blkburn/cc2652_zigbee_zed/zed_sensor_cc2652/Stack/ZStackTask/zstack.h

#define ZSTACK_H
#include <stdbool.h>
#include <stdint.h>
#include "zglobals.h"
#include "nl_mede.h"
#include "bdb_interface.h"
#if !defined (DISABLE_GREENPOWER_BASIC_PROXY) && (ZG_BUILD_RTR_TYPE)
#include "cgp_stub.h"
#endif
#if defined ( BDB_TL_INITIATOR ) || defined ( BDB_TL_TARGET )
#include "bdb_touchlink.h"
#include "bdb_tl_commissioning.h"
#endif
#ifdef __cplusplus
extern "C"
{
#endif
#define EXTADDR_LEN 8
#define DEFAULT_RADIUS  30
#if ZG_BUILD_COORDINATOR_TYPE
#define DEFAULT_COMISSIONING_MODE (BDB_COMMISSIONING_MODE_NWK_STEERING | BDB_COMMISSIONING_MODE_NWK_FORMATION | BDB_COMMISSIONING_MODE_FINDING_BINDING)
#else
#define DEFAULT_COMISSIONING_MODE (BDB_COMMISSIONING_MODE_NWK_STEERING | BDB_COMMISSIONING_MODE_FINDING_BINDING)
#endif
#define BDB_COMMISSIONING_MODE_INITIATOR_TL         (1<<0)
#define BDB_COMMISSIONING_MODE_NWK_STEERING         (1<<1)
#define BDB_COMMISSIONING_MODE_NWK_FORMATION        (1<<2)
#define BDB_COMMISSIONING_MODE_FINDING_BINDING      (1<<3)
typedef enum
{
  zstack_UseDefaultGlobalTrustCenterLinkKey,
  zstack_UseInstallCode,
  zstack_UseInstallCodeWithFallback,
  zstack_UseAPSKey,
  zstack_UseAPSKeyWithFallback,
}zstack_CentralizedLinkKeyModes_t;
typedef enum
{
    zstack_ZStatusValues_ZSuccess = 0x00,
    zstack_ZStatusValues_ZFailure = 0x01,
    zstack_ZStatusValues_ZInvalidParameter = 0x02,
    zstack_ZStatusValues_ZDecodeError = 0x03,
    zstack_ZStatusValues_ZMemError = 0x10,
    zstack_ZStatusValues_ZBufferFull = 0x11,
    zstack_ZStatusValues_ZUnsupportedMode = 0x12,
    zstack_ZStatusValues_ZMacMemError = 0x13,
    zstack_ZStatusValues_ZSapiInProgress = 0x20,
    zstack_ZStatusValues_ZSapiTimeout = 0x21,
    zstack_ZStatusValues_ZSapiInit = 0x22,
    zstack_ZStatusValues_ZNotAuthorized = 0x7E,
    zstack_ZStatusValues_ZMalformedCmd = 0x80,
    zstack_ZStatusValues_ZUnsupClusterCmd = 0x81,
    zstack_ZStatusValues_ZOtaAbort = 0x95,
    zstack_ZStatusValues_ZOtaImageInvalid = 0x96,
    zstack_ZStatusValues_ZOtaWaitForData = 0x97,
    zstack_ZStatusValues_ZOtaNoImageAvailable = 0x98,
    zstack_ZStatusValues_ZOtaRequireMoreImage = 0x99,
    zstack_ZStatusValues_ZApsFail = 0xb1,
    zstack_ZStatusValues_ZApsTableFull = 0xb2,
    zstack_ZStatusValues_ZApsIllegalRequest = 0xb3,
    zstack_ZStatusValues_ZApsInvalidBinding = 0xb4,
    zstack_ZStatusValues_ZApsUnsupportedAttrib = 0xb5,
    zstack_ZStatusValues_ZApsNotSupported = 0xb6,
    zstack_ZStatusValues_ZApsNoAck = 0xb7,
    zstack_ZStatusValues_ZApsDuplicateEntry = 0xb8,
    zstack_ZStatusValues_ZApsNoBoundDevice = 0xb9,
    zstack_ZStatusValues_ZApsNotAllowed = 0xba,
    zstack_ZStatusValues_ZApsNotAuthenticated = 0xbb,
    zstack_ZStatusValues_ZSecNoKey = 0xa1,
    zstack_ZStatusValues_ZSecOldFrmCount = 0xa2,
    zstack_ZStatusValues_ZSecMaxFrmCount = 0xa3,
    zstack_ZStatusValues_ZSecCcmFail = 0xa4,
    zstack_ZStatusValues_ZNwkInvalidParam = 0xc1,
    zstack_ZStatusValues_ZNwkInvalidRequest = 0xc2,
    zstack_ZStatusValues_ZNwkNotPermitted = 0xc3,
    zstack_ZStatusValues_ZNwkStartupFailure = 0xc4,
    zstack_ZStatusValues_ZNwkAlreadyPresent = 0xc5,
    zstack_ZStatusValues_ZNwkSyncFailure = 0xc6,
    zstack_ZStatusValues_ZNwkTableFull = 0xc7,
    zstack_ZStatusValues_ZNwkUnknownDevice = 0xc8,
    zstack_ZStatusValues_ZNwkUnsupportedAttribute = 0xc9,
    zstack_ZStatusValues_ZNwkNoNetworks = 0xca,
    zstack_ZStatusValues_ZNwkLeaveUnconfirmed = 0xcb,
    zstack_ZStatusValues_ZNwkNoAck = 0xcc,
    zstack_ZStatusValues_ZNwkNoRoute = 0xcd,
    zstack_ZStatusValues_ZAfDuplicateEndpoint = 0xd0,
    zstack_ZStatusValues_ZAfEndpointMax = 0xd1,
    zstack_ZStatusValues_ZIcallNoMsg = 0x30,
    zstack_ZStatusValues_ZIcallTimeout = 0x31
} zstack_ZStatusValues;
typedef enum
{
    zstack_AFAddrMode_NONE = 0,
    zstack_AFAddrMode_GROUP = 1,
    zstack_AFAddrMode_SHORT = 2,
    zstack_AFAddrMode_EXT = 3,
    zstack_AFAddrMode_BROADCAST = 15,
} zstack_AFAddrMode;
typedef enum
{
    zstack_ResetTypes_DEVICE = 0,
    zstack_ResetTypes_SERIAL_BOOTLOADER = 1,
} zstack_ResetTypes;
typedef enum
{
    zstack_ResetReasons_POWERUP = 0,
    zstack_ResetReasons_EXTERNAL = 1,
    zstack_ResetReasons_WATCHDOG = 2,
} zstack_ResetReasons;
typedef enum
{
    zstack_LogicalTypes_COORDINATOR = 0,
    zstack_LogicalTypes_ROUTER = 1,
    zstack_LogicalTypes_ENDDEVICE = 2,
    zstack_LogicalTypes_UNKNOWN = 3,
} zstack_LogicalTypes;
typedef enum
{
    zstack_NetworkLatency_NO_LATENCY_REQS = 0,
    zstack_NetworkLatency_FAST_BEACONS = 1,
    zstack_NetworkLatency_SLOW_BEACONDS = 2,
} zstack_NetworkLatency;
typedef enum
{
    zstack_NwkAddrReqType_SINGLE_DEVICE = 0,
    zstack_NwkAddrReqType_EXTENDED_W_ASSOCDEVS = 1,
} zstack_NwkAddrReqType;
typedef enum
{
    zstack_PowerLevel_LEVEL_CRITICAL = 0x00,
    zstack_PowerLevel_LEVEL_33 = 0x04,
    zstack_PowerLevel_LEVEL_66 = 0x08,
    zstack_PowerLevel_LEVEL_100 = 0x0C,
} zstack_PowerLevel;
typedef enum
{
    zstack_PowerModes_POWER_SYNCHRONIZED = 0,
    zstack_PowerModes_POWER_PERIODIC = 1,
    zstack_PowerModes_POWER_STIMULATED = 2,
} zstack_PowerModes;
typedef enum
{
    zstack_ZdpStatus_SUCCESS = 0,
    zstack_ZdpStatus_INVALID_REQTYPE = 0x80,
    zstack_ZdpStatus_DEVICE_NOT_FOUND = 0x81,
    zstack_ZdpStatus_INVALID_EP = 0x82,
    zstack_ZdpStatus_NOT_ACTIVE = 0x83,
    zstack_ZdpStatus_NOT_SUPPORTED = 0x84,
    zstack_ZdpStatus_TIMEOUT = 0x85,
    zstack_ZdpStatus_NO_MATCH = 0x86,
    zstack_ZdpStatus_NO_ENTRY = 0x88,
    zstack_ZdpStatus_NO_DESCRIPTOR = 0x89,
    zstack_ZdpStatus_INSUFFICIENT_SPACE = 0x8a,
    zstack_ZdpStatus_NOT_PERMITTED = 0x8b,
    zstack_ZdpStatus_TABLE_FULL = 0x8c,
    zstack_ZdpStatus_NOT_AUTHORIZED = 0x8d,
    zstack_ZdpStatus_BINDING_TABLE_FULL = 0x8e,
} zstack_ZdpStatus;
typedef enum
{
    zstack_DevState_HOLD = 0,
    zstack_DevState_INIT = 1,
    zstack_DevState_NWK_DISC = 2,
    zstack_DevState_NWK_JOINING = 3,
    zstack_DevState_NWK_REJOIN_SEC_CURR_CHANNEL = 4,
    zstack_DevState_END_DEVICE_UNAUTH = 5,
    zstack_DevState_DEV_END_DEVICE = 6,
    zstack_DevState_DEV_ROUTER = 7,
    zstack_DevState_COORD_STARTING = 8,
    zstack_DevState_DEV_ZB_COORD = 9,
    zstack_DevState_NWK_ORPHAN = 10,
    zstack_DevState_NWK_KA = 11,
    zstack_DevState_NWK_BACKOFF = 12,
    zstack_DevState_NWK_REJOIN_SEC_ALL_CHANNEL = 13,
    zstack_DevState_NWK_TC_REJOIN_CURR_CHANNEL = 14,
    zstack_DevState_NWK_TC_REJOIN_ALL_CHANNEL = 15,
} zstack_DevState;
typedef enum
{
    zstack_NwkState_INIT = 0,
    zstack_NwkState_JOINING_ORPHAN = 1,
    zstack_NwkState_DISC = 2,
    zstack_NwkState_JOINING = 3,
    zstack_NwkState_ENDDEVICE = 4,
    zstack_NwkState_PAN_CHNL_SELECTION = 5,
    zstack_NwkState_PAN_CHNL_VERIFY = 6,
    zstack_NwkState_STARTING = 7,
    zstack_NwkState_ROUTER = 8,
    zstack_NwkState_REJOINING = 9,
} zstack_NwkState;
typedef enum
{
    zstack_RouteStatus_ROUTE_ACTIVE = 0,
    zstack_RouteStatus_ROUTE_DISCOVERY_UNDERWAY = 1,
    zstack_RouteStatus_ROUTE_DISCOVERY_FAILED = 2,
    zstack_RouteStatus_ROUTE_INACTIVE = 3,
    zstack_RouteStatus_ROUTE_VALIDATION_UNDERWAY = 4,
} zstack_RouteStatus;
typedef enum
{
    zstack_RxOnWhenIdleTypes_OFF = 0,
    zstack_RxOnWhenIdleTypes_ON = 1,
    zstack_RxOnWhenIdleTypes_UNKNOWN = 2,
} zstack_RxOnWhenIdleTypes;
typedef enum
{
    zstack_RelationTypes_PARENT = 0,
    zstack_RelationTypes_CHILD = 1,
    zstack_RelationTypes_SIBLING = 2,
    zstack_RelationTypes_UNKNOWN = 3,
    zstack_RelationTypes_PREVIOUS_CHILD = 4,
} zstack_RelationTypes;
typedef enum
{
    zstack_PermitJoinTypes_NOT_ACCEPTING_JOIN = 0,
    zstack_PermitJoinTypes_ACCEPTING_JOIN = 1,
    zstack_PermitJoinTypes_UNKNOWN_JOIN = 2,
} zstack_PermitJoinTypes;
typedef enum
{
    zstack_BuildTypes_COORDINATOR = 0,
    zstack_BuildTypes_ROUTER = 1,
    zstack_BuildTypes_ENDDEVICE = 2,
    zstack_BuildTypes_ALLBUILD = 3,
} zstack_BuildTypes;
typedef uint8_t zstack_LongAddr_t[EXTADDR_LEN];
typedef struct _zstack_afaddr_t
{
    zstack_AFAddrMode addrMode;
    union
    {
        uint16_t shortAddr;
        zstack_LongAddr_t extAddr;
    } addr;
    uint8_t endpoint;
    uint16_t panID;
} zstack_AFAddr_t;
typedef struct _zstack_startupoptions_t
{
    bool clearState;
    bool clearConfig;
} zstack_StartupOptions_t;
typedef struct _zstack_simpledescriptor_t
{
    uint8_t endpoint;
    uint16_t profileID;
    uint16_t deviceID;
    uint8_t deviceVer;
    uint8_t n_inputClusters;
    uint16_t *pInputClusters;
    uint8_t n_outputClusters;
    uint16_t *pOutputClusters;
} zstack_SimpleDescriptor_t;
typedef struct _zstack_transoptions_t
{
    bool wildcardProfileID;
    bool ackRequest;
    bool limitConcentrator;
    bool suppressRouteDisc;
    bool apsSecurity;
    bool skipRouting;
} zstack_TransOptions_t;
typedef struct _zstack_capabilityinfo_t
{
    bool panCoord;
    bool ffd;
    bool mainsPower;
    bool rxOnWhenIdle;
    bool security;
} zstack_CapabilityInfo_t;
typedef struct _zstack_servercapabilities_t
{
    bool primaryTrustCenter;
    bool backupTrustCenter;
    bool primaryBindingTableCache;
    bool backupBindingTableCache;
    bool primaryDiscoveryCache;
    bool backupDiscoveryCache;
    bool networkManager;
} zstack_ServerCapabilities_t;
typedef struct _zstack_bindrec_t
{
    zstack_LongAddr_t srcAddr;
    uint8_t srcEndpoint;
    uint16_t clusterID;
    zstack_AFAddr_t dstAddr;
} zstack_BindRec_t;
typedef struct _zstack_leaveoptions_t
{
    bool rejoin;
    bool removeChildren;
} zstack_LeaveOptions_t;
typedef struct _zstack_nodedescriptor_t
{
    zstack_LogicalTypes logicalType;
    bool complexDescAvail;
    bool userDescAvail;
    uint8_t apsFlags;
    uint8_t freqBand;
    zstack_CapabilityInfo_t capInfo;
    uint16_t manufacturerCode;
    uint8_t maxBufferSize;
    uint16_t maxInTransferSize;
    zstack_ServerCapabilities_t serverMask;
    uint16_t maxOutTransferSize;
    uint32_t descCap;
} zstack_NodeDescriptor_t;
typedef struct _zstack_powersource_t
{
    bool mains;
    bool recharge;
    bool dispose;
} zstack_PowerSource_t;
typedef struct _zstack_powerdescriptor_t
{
    zstack_PowerModes powerMode;
    zstack_PowerSource_t availPowerSource;
    zstack_PowerSource_t currentPowerSource;
    zstack_PowerLevel currentPowerLevel;
} zstack_PowerDescriptor_t;
typedef struct _zstack_nwkdiscitem_t
{
    zstack_LongAddr_t extendedPANID;
    uint8_t logicalChan;
    uint8_t stackProfile;
    uint8_t version;
    uint8_t beaconOrder;
    uint8_t superFrameOrder;
    bool permitJoin;
} zstack_nwkDiscItem_t;
typedef struct _zstack_nwklqiitem_t
{
    uint16_t nwkAddr;
    uint16_t panID;
    zstack_LongAddr_t extendedPANID;
    zstack_LongAddr_t extendedAddr;
    uint8_t rxLqi;
    zstack_LogicalTypes deviceType;
    zstack_RxOnWhenIdleTypes rxOnWhenIdle;
    zstack_RelationTypes relationship;
    uint8_t depth;
    zstack_PermitJoinTypes permit;
} zstack_nwkLqiItem_t;
typedef struct _zstack_routeitem_t
{
    uint16_t dstAddr;
    uint16_t nextHop;
    zstack_RouteStatus status;
    bool memoryConstrained;
    bool manyToOne;
    bool routeRecordRequired;
} zstack_routeItem_t;
typedef struct _zstack_binditem_t
{
    zstack_LongAddr_t srcAddr;
    uint8_t srcEndpoint;
    uint16_t clustedID;
    zstack_AFAddr_t dstAddr;
} zstack_bindItem_t;
typedef struct _zstack_devicetypes_t
{
    bool coodinator;
    bool router;
    bool enddevice;
} zstack_deviceTypes_t;
typedef struct _zstack_sysresetreq_t
{
    zstack_ResetTypes type;
    bool newNwkState;
} zstack_sysResetReq_t;
typedef struct _zstack_sysconfigreadreq_t
{
    bool preConfigKeyEnable;
    bool securityModeEnable;
    bool useDefaultTCLK;
    bool disabledPollRate;
    bool pollRate;
    bool apsAckWaitDuration;
    bool bindingTime;
    bool panID;
    bool maxMissingMacAckLinkFailure;
    bool indirectMsgTimeout;
    bool apsFrameRetries;
    bool bcastRetries;
    bool passiveAckTimeout;
    bool bcastDeliveryTime;
    bool routeExpiryTime;
    bool userDesc;
    bool preConfigKey;
    bool chanList;
    bool multicastRadius;
    bool extendedPANID;
    bool ieeeAddr;
    bool macRxOnIdle;
    bool snifferFeature;
    bool concentratorEnable;
    bool concentratorDiscTime;
    bool nwkUseMultiCast;
    bool devPartOfNetwork;
} zstack_sysConfigReadReq_t;
typedef struct _zstack_sysconfigwritereq_t
{
    bool has_preConfigKeyEnable;
    bool preConfigKeyEnable;
    bool has_securityModeEnable;
    bool securityModeEnable;
    bool has_useDefaultTCLK;
    bool useDefaultTCLK;
    bool has_disablePollRate;
    bool disablePollRate;
    bool has_pollRate;
    uint32_t pollRate;
    uint16_t pollRateType;
    bool has_apsAckWaitDuration;
    uint16_t apsAckWaitDuration;
    bool has_bindingTime;
    uint16_t bindingTime;
    bool has_panID;
    uint16_t panID;
    bool has_maxMissingMacAckLinkFailure;
    uint8_t maxMissingMacAckLinkFailure;
    bool has_indirectMsgTimeout;
    uint8_t indirectMsgTimeout;
    bool has_apsFrameRetries;
    uint8_t apsFrameRetries;
    bool has_bcastRetries;
    uint8_t bcastRetries;
    bool has_passiveAckTimeout;
    uint8_t passiveAckTimeout;
    bool has_bcastDeliveryTime;
    uint8_t bcastDeliveryTime;
    bool has_routeExpiryTime;
    uint8_t routeExpiryTime;
    bool has_userDesc;
    uint8_t n_userDesc;
    uint8_t *pUserDesc;
    bool has_preConfigKey;
    uint8_t n_preConfigKey;
    uint8_t *pPreConfigKey;
    bool has_chanList;
    uint32_t chanList;
    bool has_multicastRadius;
    uint8_t multicastRadius;
    bool has_extendedPANID;
    zstack_LongAddr_t extendedPANID;
    bool has_ieeeAddr;
    zstack_LongAddr_t ieeeAddr;
    bool has_macRxOnIdle;
    bool macRxOnIdle;
    bool has_snifferFeature;
    bool snifferFeature;
    bool has_concentratorEnable;
    bool concentratorEnable;
    bool has_concentratorDiscTime;
    uint8_t concentratorDiscTime;
    bool has_nwkUseMultiCast;
    bool nwkUseMultiCast;
} zstack_sysConfigWriteReq_t;
typedef struct _zstack_syssettxpowerreq_t
{
    int_least8_t requestedTxPower;
} zstack_sysSetTxPowerReq_t;
typedef struct _zstack_sysversionrsp_t
{
    uint8_t transportRev;
    zstack_BuildTypes product;
    uint8_t majorRel;
    uint8_t minorRel;
    uint8_t maintRel;
} zstack_sysVersionRsp_t;
typedef struct _zstack_sysconfigreadrsp_t
{
    bool has_preConfigKeyEnable;
    bool preConfigKeyEnable;
    bool has_securityModeEnable;
    bool securityModeEnable;
    bool has_useDefaultTCLK;
    bool useDefaultTCLK;
    bool has_disabledPollRateState;
    bool disabledPollRate;
    bool has_pollRate;
    uint32_t CurrentPollRate;
    uint16_t CurrentPollRateTypesEnabled;
    uint32_t PollRateDefault;
    uint32_t PollRateApp1;
    uint32_t PollRateApp2;
    uint32_t PollRateJoinRejoin;
    uint32_t PollRateQueue;
    uint32_t PollRateResponse;
    bool has_apsAckWaitDuration;
    uint16_t apsAckWaitDuration;
    bool has_bindingTime;
    uint16_t bindingTime;
    bool has_panID;
    uint16_t panID;
    bool has_maxMissingMacAckLinkFailure;
    uint8_t maxMissingMacAckLinkFailure;
    bool has_indirectMsgTimeout;
    uint8_t indirectMsgTimeout;
    bool has_apsFrameRetries;
    uint8_t apsFrameRetries;
    bool has_bcastRetries;
    uint8_t bcastRetries;
    bool has_passiveAckTimeout;
    uint8_t passiveAckTimeout;
    bool has_bcastDeliveryTime;
    uint8_t bcastDeliveryTime;
    bool has_routeExpiryTime;
    uint8_t routeExpiryTime;
    bool has_userDesc;
    uint8_t n_userDesc;
    uint8_t *pUserDesc;
    bool has_preConfigKey;
    uint8_t *pPreConfigKey;
    bool has_chanList;
    uint32_t chanList;
    bool has_multicastRadius;
    uint8_t multicastRadius;
    bool has_extendedPANID;
    zstack_LongAddr_t extendedPANID;
    bool has_ieeeAddr;
    zstack_LongAddr_t ieeeAddr;
    bool has_macRxOnIdle;
    bool macRxOnIdle;
    bool has_snifferFeature;
    bool snifferFeature;
    bool has_concentratorEnable;
    bool concentratorEnable;
    bool has_concentratorDiscTime;
    uint8_t concentratorDiscTime;
    bool has_nwkUseMultiCast;
    bool nwkUseMultiCast;
    bool has_devPartOfNetwork;
    bool devPartOfNetwork;
} zstack_sysConfigReadRsp_t;
typedef struct _zstack_syssettxpowerrsp_t
{
    int_least8_t txPower;
} zstack_sysSetTxPowerRsp_t;
typedef struct _zstack_sysnwkinforeadrsp_t
{
    uint16_t nwkAddr;
    zstack_LongAddr_t ieeeAddr;
    zstack_DevState devState;
    uint16_t panId;
    zstack_LongAddr_t extendedPanId;
    uint16_t parentNwkAddr;
    zstack_LongAddr_t parentExtAddr;
    zstack_deviceTypes_t devTypes;
    uint8_t logicalChannel;
    zstack_CapabilityInfo_t capInfo;
} zstack_sysNwkInfoReadRsp_t;
typedef struct _zstack_sysAppMsg_t
{
    uint8_t dstEndpoint;
    uint8_t appDataLen;
    uint8_t *pAppData;
} zstack_sysAppMsg_t;
typedef struct _zstack_sysOtaMsg_t
{
    uint8_t cmd;
    uint8_t *pData;
} zstack_sysOtaMsg_t;
typedef struct _zstack_devstartreq_t
{
    uint16_t startDelay;
} zstack_devStartReq_t;
typedef struct _zstack_devnwkdiscreq_t
{
    uint32_t scanChannels;
    uint8_t scanDuration;
} zstack_devNwkDiscReq_t;
typedef struct zstack_setnwkframefwdnotificationreq_t
{
    uint8_t Enabled;
} zstack_setNwkFrameFwdNotificationReq_t;
typedef struct _zstack_devjoinreq_t
{
    uint8_t logicalChannel;
    uint16_t panID;
    zstack_LongAddr_t extendedPANID;
    uint16_t chosenParent;
    uint8_t parentDepth;
    uint8_t stackProfile;
} zstack_devJoinReq_t;
typedef struct _zstack_devrejoinreq_t
{
    bool unsecure;
    uint8_t logicalChannel;
    zstack_LongAddr_t extendedPANID;
} zstack_devRejoinReq_t;
typedef struct _zstack_devzdocbreq_t
{
    bool has_srcRtgIndCB;
    bool srcRtgIndCB;
    bool has_concentratorIndCb;
    bool concentratorIndCb;
    bool has_nwkDiscCnfCB;
    bool nwkDiscCnfCB;
    bool has_beaconNotIndCB;
    bool beaconNotIndCB;
    bool has_joinCnfCB;
    bool joinCnfCB;
    bool has_leaveCnfCB;
    bool leaveCnfCB;
    bool has_leaveIndCB;
    bool leaveIndCB;
    bool has_nwkAddrRsp;
    bool nwkAddrRsp;
    bool has_ieeeAddrRsp;
    bool ieeeAddrRsp;
    bool has_nodeDescRsp;
    bool nodeDescRsp;
    bool has_powerDescRsp;
    bool powerDescRsp;
    bool has_simpleDescRsp;
    bool simpleDescRsp;
    bool has_activeEndpointRsp;
    bool activeEndpointRsp;
    bool has_matchDescRsp;
    bool matchDescRsp;
    bool has_complexDescRsp;
    bool complexDescRsp;
    bool has_userDescRsp;
    bool userDescRsp;
    bool has_discoveryCacheRsp;
    bool discoveryCacheRsp;
    bool has_userDescCnf;
    bool userDescCnf;
    bool has_serverDiscoveryRsp;
    bool serverDiscoveryRsp;
    bool has_bindRsp;
    bool bindRsp;
    bool has_endDeviceBindRsp;
    bool endDeviceBindRsp;
    bool has_unbindRsp;
    bool unbindRsp;
    bool has_mgmtNwkDiscRsp;
    bool mgmtNwkDiscRsp;
    bool has_mgmtLqiRsp;
    bool mgmtLqiRsp;
    bool has_mgmtRtgRsp;
    bool mgmtRtgRsp;
    bool has_mgmtBindRsp;
    bool mgmtBindRsp;
    bool has_mgmtLeaveRsp;
    bool mgmtLeaveRsp;
    bool has_mgmtDirectJoinRsp;
    bool mgmtDirectJoinRsp;
    bool has_mgmtPermitJoinRsp;
    bool mgmtPermitJoinRsp;
    bool has_mgmtNwkUpdateNotify;
    bool mgmtNwkUpdateNotify;
    bool has_deviceAnnounce;
    bool deviceAnnounce;
    bool has_devStateChange;
    bool devStateChange;
    bool has_devJammerInd;
    bool devJammerInd;
    bool has_tcDeviceInd;
    bool tcDeviceInd;
    bool has_devPermitJoinInd;
    bool devPermitJoinInd;
} zstack_devZDOCBReq_t;
typedef struct _zstack_devnwkroutereq_t
{
    uint16_t dstAddr;
    bool mtoRoute;
    bool mtoNoCache;
    bool multicast;
    uint8_t radius;
} zstack_devNwkRouteReq_t;
typedef struct _zstack_devnwkcheckroutereq_t
{
    uint16_t dstAddr;
    bool mtoRoute;
} zstack_devNwkCheckRouteReq_t;
typedef struct _zstack_devjammerind_t
{
    bool jammed;
} zstack_devJammerInd_t;
typedef struct _zstack_devpermitjoinind_t
{
    uint8_t duration;
} zstack_devPermitJoinInd_t;
typedef struct _zstack_devupdateneighbortxcostreq_t
{
    uint16_t nwkAddr;
    uint16_t panID;
    uint8_t txCost;
} zstack_devUpdateNeighborTxCostReq_t;
typedef struct _zstack_devforcenetworksettingsreq_t
{
    zstack_NwkState state;
    uint16_t nwkAddr;
    uint32_t channelList;
    uint16_t parentNwkAddr;
    uint16_t panID;
    uint8_t depth;
    uint8_t maxRouters;
    uint8_t maxChildren;
    uint32_t allocatedRouterAddresses;
    uint32_t allocatedEndDeviceAddresses;
    uint8_t updateID;
    zstack_LongAddr_t extendedPANID;
} zstack_devForceNetworkSettingsReq_t;
typedef struct _zstack_devforcenetworkupdatereq_t
{
    uint8_t updateID;
    uint8_t logicalChannel;
} zstack_devForceNetworkUpdateReq_t;
typedef struct _zstack_devforcemacparamsreq_t
{
    uint16_t nwkAddr;
    uint16_t panID;
    uint8_t logicalChannel;
} zstack_devForceMacParamsReq_t;
typedef struct _zstack_apsremovegroup_t
{
    uint8_t endpoint;
    uint16_t groupID;
} zstack_apsRemoveGroup_t;
typedef struct _zstack_apsremoveallgroups_t
{
    uint8_t endpoint;
} zstack_apsRemoveAllGroups_t;
typedef struct _zstack_apsfindallgroupsreq_t
{
    uint8_t endpoint;
} zstack_apsFindAllGroupsReq_t;
typedef struct _zstack_apsfindallgroupsrsp_t
{
    uint8_t numGroups;
    uint16_t *pGroupList;
} zstack_apsFindAllGroupsRsp_t;
typedef struct _zstack_apsfindgroupreq_t
{
    uint8_t endpoint;
    uint16_t groupID;
} zstack_apsFindGroupReq_t;
typedef struct _zstack_apsfindgrouprsp_t
{
    uint16_t groupID;
    uint8_t n_name;
    uint8_t *pName;
} zstack_apsFindGroupRsp_t;
typedef struct _zstack_apsaddgroup_t
{
    uint8_t endpoint;
    uint16_t groupID;
    uint8_t n_name;
    uint8_t *pName;
} zstack_apsAddGroup_t;
typedef struct _zstack_afregisterreq_t
{
    uint8_t endpoint;
    zstack_SimpleDescriptor_t *pSimpleDesc;
    zstack_NetworkLatency latencyReq;
} zstack_afRegisterReq_t;
typedef struct _zstack_afunregisterreq_t
{
    uint8_t endpoint;
} zstack_afUnRegisterReq_t;
typedef struct _zstack_afdatareq_t
{
    zstack_AFAddr_t dstAddr;
    uint8_t n_relayList;
    uint16_t *pRelayList;
    uint8_t srcEndpoint;
    uint16_t clusterID;
    uint8_t *transID;
    zstack_TransOptions_t options;
    uint8_t radius;
    uint16_t n_payload;
    uint8_t *pPayload;
} zstack_afDataReq_t;
typedef struct _zstack_afinterpanctlreq_t
{
    bool enable;
    bool has_channel;
    uint8_t channel;
    bool has_endpoint;
    uint8_t endpoint;
    bool has_panID;
    uint16_t panID;
} zstack_afInterPanCtlReq_t;
typedef struct _zstack_afconfiggetreq_t
{
    uint8_t endpoint;
} zstack_afConfigGetReq_t;
typedef struct _zstack_afconfigsetreq_t
{
    uint8_t endpoint;
    uint8_t frameDelay;
    uint8_t windowSize;
} zstack_afConfigSetReq_t;
typedef struct _zstack_afconfiggetrsp_t
{
    uint8_t endpoint;
    uint8_t frameDelay;
    uint8_t windowSize;
} zstack_afConfigGetRsp_t;
typedef struct _zstack_afdataconfirmind_t
{
    zstack_ZStatusValues status;
    uint8_t endpoint;
    uint8_t transID;
    uint16_t clusterID;
} zstack_afDataConfirmInd_t;
typedef struct _zstack_afincomingmsgind_t
{
    zstack_AFAddr_t srcAddr;
    uint16_t groupID;
    uint16_t clusterId;
    uint16_t macDestAddr;
    uint8_t endpoint;
    bool wasBroadcast;
    bool securityUse;
    uint8_t linkQuality;
    uint8_t correlation;
    int_least8_t rssi;
    uint32_t timestamp;
    uint8_t nwkSeqNum;
    uint16_t macSrcAddr;
    uint8_t radius;
    uint8_t n_payload;
    uint8_t *pPayload;
} zstack_afIncomingMsgInd_t;
typedef struct _zstack_afreflecterrorind_t
{
    zstack_ZStatusValues status;
    zstack_AFAddr_t dstAddr;
    uint8_t transID;
} zstack_afReflectErrorInd_t;
typedef struct _zstack_zdonwkaddrreq_t
{
    zstack_LongAddr_t ieeeAddr;
    zstack_NwkAddrReqType type;
    uint8_t startIndex;
} zstack_zdoNwkAddrReq_t;
typedef struct _zstack_zdoieeeaddrreq_t
{
    uint16_t nwkAddr;
    zstack_NwkAddrReqType type;
    uint8_t startIndex;
} zstack_zdoIeeeAddrReq_t;
typedef struct _zstack_zdonodedescreq_t
{
    uint16_t dstAddr;
    uint16_t nwkAddrOfInterest;
} zstack_zdoNodeDescReq_t;
typedef struct _zstack_zdopowerdescreq_t
{
    uint16_t dstAddr;
    uint16_t nwkAddrOfInterest;
} zstack_zdoPowerDescReq_t;
typedef struct _zstack_zdosimpledescreq_t
{
    uint16_t dstAddr;
    uint16_t nwkAddrOfInterest;
    uint8_t endpoint;
} zstack_zdoSimpleDescReq_t;
typedef struct _zstack_zdoactiveendpointreq_t
{
    uint16_t dstAddr;
    uint16_t nwkAddrOfInterest;
} zstack_zdoActiveEndpointReq_t;
typedef struct _zstack_zdomatchdescreq_t
{
    uint16_t dstAddr;
    uint16_t nwkAddrOfInterest;
    uint16_t profileID;
    uint8_t n_inputClusters;
    uint16_t *pInputClusters;
    uint8_t n_outputClusters;
    uint16_t *pOutputClusters;
} zstack_zdoMatchDescReq_t;
typedef struct _zstack_zdocomplexdescreq_t
{
    uint16_t dstAddr;
    uint16_t nwkAddrOfInterest;
} zstack_zdoComplexDescReq_t;
typedef struct _zstack_zdouserdescreq_t
{
    uint16_t dstAddr;
    uint16_t nwkAddrOfInterest;
} zstack_zdoUserDescReq_t;
typedef struct _zstack_zdosetbindunbindauthaddrreq_t
{
    zstack_LongAddr_t AuthAddress;
    uint16_t ClusterId;
    uint8_t  Endpoint;
} zstack_zdoSetBindUnbindAuthAddr_t;
typedef struct _zstack_zdodeviceannouncereq_t
{
    uint16_t nwkAddr;
    zstack_LongAddr_t ieeeAddr;
    zstack_CapabilityInfo_t capabilities;
} zstack_zdoDeviceAnnounceReq_t;
typedef struct _zstack_zdouserdescsetreq_t
{
    uint16_t dstAddr;
    uint16_t nwkAddrOfInterest;
    uint8_t n_userDescriptor;
    uint8_t *pUserDescriptor;
} zstack_zdoUserDescSetReq_t;
typedef struct _zstack_zdoserverdiscreq_t
{
    zstack_ServerCapabilities_t serverMask;
} zstack_zdoServerDiscReq_t;
typedef struct _zstack_zdoenddevicebindreq_t
{
    uint16_t dstAddr;
    uint16_t bindingTarget;
    uint8_t endpoint;
    uint16_t profileID;
    uint8_t n_inputClusters;
    uint16_t *pInputClusters;
    uint8_t n_outputClusters;
    uint16_t *pOutputClusters;
} zstack_zdoEndDeviceBindReq_t;
typedef struct _zstack_zdobindreq_t
{
    uint16_t nwkAddr;
    zstack_BindRec_t bindInfo;
} zstack_zdoBindReq_t;
typedef struct _zstack_zdounbindreq_t
{
    uint16_t nwkAddr;
    zstack_BindRec_t bindInfo;
} zstack_zdoUnbindReq_t;
typedef struct _zstack_zdomgmtnwkdiscreq_t
{
    uint16_t nwkAddr;
    uint32_t scanChannels;
    uint8_t scanDuration;
    uint8_t startIndex;
} zstack_zdoMgmtNwkDiscReq_t;
typedef struct _zstack_zdomgmtlqireq_t
{
    uint16_t nwkAddr;
    uint8_t startIndex;
} zstack_zdoMgmtLqiReq_t;
typedef struct _zstack_zdomgmtrtgreq_t
{
    uint16_t nwkAddr;
    uint8_t startIndex;
} zstack_zdoMgmtRtgReq_t;
typedef struct _zstack_zdomgmtbindreq_t
{
    uint16_t nwkAddr;
    uint8_t startIndex;
} zstack_zdoMgmtBindReq_t;
typedef struct _zstack_zdomgmtleavereq_t
{
    uint16_t nwkAddr;
    zstack_LongAddr_t deviceAddress;
    zstack_LeaveOptions_t options;
} zstack_zdoMgmtLeaveReq_t;
typedef struct _zstack_zdomgmtdirectjoinreq_t
{
    uint16_t nwkAddr;
    zstack_LongAddr_t deviceAddress;
    zstack_CapabilityInfo_t capInfo;
} zstack_zdoMgmtDirectJoinReq_t;
typedef struct _zstack_zdomgmtpermitjoinreq_t
{
    uint16_t nwkAddr;
    uint8_t duration;
    bool tcSignificance;
} zstack_zdoMgmtPermitJoinReq_t;
typedef struct _zstack_zdomgmtnwkupdatereq_t
{
    uint16_t dstAddr;
    uint32_t channelMask;
    uint8_t scanDuration;
    uint8_t scanCount;
    uint8_t nwkUpdateId;
    uint16_t nwkMgrAddr;
} zstack_zdoMgmtNwkUpdateReq_t;
typedef struct _zstack_zdonwkaddrrspind_t
{
    zstack_ZdpStatus status;
    zstack_LongAddr_t ieeeAddr;
    uint16_t nwkAddr;
    uint8_t startIndex;
    uint8_t n_assocDevList;
    uint16_t *pAssocDevList;
} zstack_zdoNwkAddrRspInd_t;
typedef struct _zstack_zdoieeeaddrrspind_t
{
    zstack_ZdpStatus status;
    zstack_LongAddr_t ieeeAddr;
    uint16_t nwkAddr;
    uint8_t startIndex;
    uint8_t n_assocDevList;
    uint16_t *pAssocDevList;
} zstack_zdoIeeeAddrRspInd_t;
typedef struct _zstack_zdonodedescrspind_t
{
    uint16_t srcAddr;
    zstack_ZdpStatus status;
    uint16_t nwkAddrOfInterest;
    zstack_NodeDescriptor_t nodeDesc;
} zstack_zdoNodeDescRspInd_t;
typedef struct _zstack_zdopowerdescrspind_t
{
    uint16_t srcAddr;
    zstack_ZdpStatus status;
    uint16_t nwkAddrOfInterest;
    zstack_PowerDescriptor_t powerDesc;
} zstack_zdoPowerDescRspInd_t;
typedef struct _zstack_zdosimpledescrspind_t
{
    uint16_t srcAddr;
    zstack_ZdpStatus status;
    uint16_t nwkAddrOfInterest;
    zstack_SimpleDescriptor_t simpleDesc;
} zstack_zdoSimpleDescRspInd_t;
typedef struct _zstack_zdoactiveendpointsrspind_t
{
    uint16_t srcAddr;
    zstack_ZdpStatus status;
    uint16_t nwkAddrOfInterest;
    uint8_t n_activeEPList;
    uint8_t *pActiveEPList;
} zstack_zdoActiveEndpointsRspInd_t;
typedef struct _zstack_zdomatchdescrspind_t
{
    uint16_t srcAddr;
    zstack_ZdpStatus status;
    uint16_t nwkAddrOfInterest;
    uint8_t n_matchList;
    uint8_t *pMatchList;
} zstack_zdoMatchDescRspInd_t;
typedef struct _zstack_zdouserdescrspind_t
{
    uint16_t srcAddr;
    zstack_ZdpStatus status;
    uint16_t nwkAddrOfInterest;
    uint8_t n_desc;
    uint8_t *pDesc;
} zstack_zdoUserDescRspInd_t;
typedef struct _zstack_zdoserverdiscoveryrspind_t
{
    uint16_t srcAddr;
    zstack_ZdpStatus status;
    zstack_ServerCapabilities_t serverCap;
} zstack_zdoServerDiscoveryRspInd_t;
typedef struct _zstack_zdobindrspind_t
{
    uint16_t srcAddr;
    zstack_ZdpStatus status;
} zstack_zdoBindRspInd_t;
typedef struct _zstack_zdoenddevicebindrspind_t
{
    uint16_t srcAddr;
    zstack_ZdpStatus status;
} zstack_zdoEndDeviceBindRspInd_t;
typedef struct _zstack_zdounbindrspind_t
{
    uint16_t srcAddr;
    zstack_ZdpStatus status;
} zstack_zdoUnbindRspInd_t;
typedef struct _zstack_zdodeviceannounceind_t
{
    uint16_t srcAddr;
    uint16_t devAddr;
    zstack_LongAddr_t devExtAddr;
    zstack_CapabilityInfo_t capInfo;
} zstack_zdoDeviceAnnounceInd_t;
typedef struct _zstack_zdomgmtnwkdiscrspind_t
{
    uint16_t srcAddr;
    zstack_ZdpStatus status;
    uint8_t networkCount;
    uint8_t startIndex;
    uint8_t n_netList;
    zstack_nwkDiscItem_t *pNetList;
} zstack_zdoMgmtNwkDiscRspInd_t;
typedef struct _zstack_zdomgmtlqirspind_t
{
    uint16_t srcAddr;
    zstack_ZdpStatus status;
    uint8_t neighborLqiEntries;
    uint8_t startIndex;
    uint8_t n_lqiList;
    zstack_nwkLqiItem_t *pLqiList;
} zstack_zdoMgmtLqiRspInd_t;
typedef struct _zstack_zdomgmtrtgrspind_t
{
    uint16_t srcAddr;
    zstack_ZdpStatus status;
    uint8_t rtgEntries;
    uint8_t startIndex;
    uint8_t n_rtgList;
    zstack_routeItem_t *pRtgList;
} zstack_zdoMgmtRtgRspInd_t;
typedef struct _zstack_zdomgmtbindrspind_t
{
    uint16_t srcAddr;
    zstack_ZdpStatus status;
    uint8_t bindEntries;
    uint8_t startIndex;
    uint8_t n_bindList;
    zstack_bindItem_t *pBindList;
} zstack_zdoMgmtBindRspInd_t;
typedef struct _zstack_zdomgmtleaverspind_t
{
    uint16_t srcAddr;
    zstack_ZdpStatus status;
} zstack_zdoMgmtLeaveRspInd_t;
typedef struct _zstack_zdomgmtdirectjoinrspind_t
{
    uint16_t srcAddr;
    zstack_ZdpStatus status;
} zstack_zdoMgmtDirectJoinRspInd_t;
typedef struct _zstack_zdomgmtpermitjoinrspind_t
{
    uint16_t srcAddr;
    zstack_ZdpStatus status;
} zstack_zdoMgmtPermitJoinRspInd_t;
typedef struct _zstack_zdomgmtnwkupdatenotifyind_t
{
    uint16_t srcAddr;
    zstack_ZdpStatus status;
    uint32_t scannedChannels;
    uint16_t totalTrans;
    uint16_t transFails;
    uint8_t n_energyValuesList;
    uint8_t *pEnergyValuesList;
} zstack_zdoMgmtNwkUpdateNotifyInd_t;
typedef struct _zstack_zdotcteviceind_t
{
    uint16_t nwkAddr;
    uint16_t parentAddr;
    zstack_LongAddr_t extendedAddr;
} zstack_zdoTcDeviceInd_t;
typedef struct _zstack_zdosrcrtgind_t
{
    uint16_t srcAddr;
    uint8_t n_relay;
    uint16_t *pRelay;
} zstack_zdoSrcRtgInd_t;
typedef struct _zstack_zdocncntrtrind_t
{
    uint16_t nwkAddr;
    uint8_t pktCost;
    zstack_LongAddr_t ieeeAddr;
} zstack_zdoCncntrtrInd_t;
typedef struct _zstack_zdonwkdisccnf_t
{
    uint8_t status;
} zstack_zdoNwkDiscCnf_t;
typedef struct _zstack_zdobeaconnotifyind_t
{
    uint16_t sourceAddr;
    uint16_t panID;
    uint8_t logicalChannel;
    bool permitJoining;
    bool routerCapacity;
    bool deviceCapacity;
    uint8_t protocolVersion;
    uint8_t stackProfile;
    uint8_t lqi;
    uint8_t depth;
    uint8_t updateID;
    zstack_LongAddr_t extendedPANID;
} zstack_zdoBeaconNotifyInd_t;
typedef struct _zstack_zdojoinconf_t
{
    uint16_t devAddr;
    uint16_t parentAddr;
} zstack_zdoJoinConf_t;
typedef struct _zstack_zdoleavecnf_t
{
    uint16_t dstAddr;
    zstack_LongAddr_t extendedAddr;
    bool removeChildren;
    bool rejoin;
} zstack_zdoLeaveCnf_t;
typedef struct _zstack_zdoleaveind_t
{
    uint16_t srcAddr;
    zstack_LongAddr_t extendedAddr;
    uint8_t request;
    bool removeChildren;
    bool rejoin;
} zstack_zdoLeaveInd_t;
typedef struct _zstack_nwkframefwdnotification_t
{
    nwkFrameFwdNotification_t nwkFrameFwdNotification;
} zstack_nwkFrameFwdNotification_t;
typedef struct _zstack_devstatechangeind_t
{
    zstack_DevState state;
} zstack_devStateChangeInd_t;
typedef struct _zstack_secnwkkeygetreq_t
{
    bool activeKey;
} zstack_secNwkKeyGetReq_t;
typedef struct _zstack_secnwkkeysetreq_t
{
    bool activeKey;
    uint8_t seqNum;
    bool has_key;
    uint8_t key[16];
} zstack_secNwkKeySetReq_t;
typedef struct _zstack_secnwkkeyupdatereq_t
{
    uint8_t* key;
    uint8_t seqNum;
    uint16_t dstAddr;
} zstack_secNwkKeyUpdateReq_t;
typedef struct _zstack_secnwkkeyswitchReq_t
{
    uint8_t seqNum;
    uint16_t dstAddr;
} zstack_secNwkKeySwitchReq_t;
typedef struct _zstack_secapslinkkeygetreq_t
{
    bool tcLinkKey;
    zstack_LongAddr_t ieeeAddr;
} zstack_secApsLinkKeyGetReq_t;
typedef struct _zstack_secapslinkkeysetreq_t
{
    bool tcLinkKey;
    uint16_t shortAddr;
    zstack_LongAddr_t ieeeAddr;
    uint8_t key[16];
    uint32_t txFrmCntr;
    uint32_t rxFrmCntr;
} zstack_secApsLinkKeySetReq_t;
typedef struct _zstack_secapslinkkeyremovereq_t
{
    bool tcLinkKey;
    zstack_LongAddr_t ieeeAddr;
} zstack_secApsLinkKeyRemoveReq_t;
typedef struct _zstack_secapsremovereq_t
{
    uint16_t parentAddr;
    uint16_t nwkAddr;
    zstack_LongAddr_t extAddr;
} zstack_secApsRemoveReq_t;
typedef struct _zstack_secmgrsetuppartnerreq_t
{
    uint16_t partNwkAddr;
    uint8_t * partExtAddr;
} zstack_secMgrSetupPartnerReq_t;
typedef struct _zstack_secmgrappkeytypesetreq_t
{
    uint8_t  keytype;
}zstack_secMgrAppKeyTypeSetReq_t;
typedef struct _zstack_secmgrappkeyreq_t
{
    uint8_t            partExtAddr[Z_EXTADDR_LEN];
}zstack_secMgrAppKeyReq_t;
typedef struct _zstack_bdbstartcommissioningreq_t
{
  uint8_t commissioning_mode;
} zstack_bdbStartCommissioningReq_t;
typedef struct _zstack_bdbsetidentifyactiveendpointreq_t
{
  uint8_t activeEndpoint;
} zstack_bdbSetIdentifyActiveEndpointReq_t;
typedef struct _zstack_bdbgetidentifyactiveendpointrsp_t
{
  uint8_t activeEndpoint;
} zstack_bdbGetIdentifyActiveEndpointRsp_t;
typedef struct _zstack_getzclframecounterrsp_t
{
  uint8_t zclFrameCounter;
}zstack_getZCLFrameCounterRsp_t;
typedef struct _zstack_bdbzclidentifycmdindreq_t
{
  uint16_t identifyTime;
  uint8_t  endpoint;
}zstack_bdbZCLIdentifyCmdIndReq_t;
typedef struct _zstack_bdbsetepdesclisttoactiveendpointrsp_t
{
  uint8_t  EndPoint;
}zstack_bdbSetEpDescListToActiveEndpointRsp_t;
typedef struct _zstack_bdbsetattributesreq_t
{
    uint32_t bdbSecondaryChannelSet;
    bool has_bdbSecondaryChannelSet;
    uint32_t bdbPrimaryChannelSet;
    bool has_bdbPrimaryChannelSet;
    uint16_t bdbCommissioningGroupID;
    bool has_bdbCommissioningGroupID;
    uint8_t bdbScanDuration;
    bool has_bdbScanDuration;
#if (ZG_BUILD_COORDINATOR_TYPE)
    bool bdbJoinUsesInstallCodeKey;
    bool has_bdbJoinUsesInstallCodeKey;
    uint8_t bdbTrustCenterNodeJoinTimeout;
    bool has_bdbTrustCenterNodeJoinTimeout;
    bool bdbTrustCenterRequireKeyExchange;
    bool has_bdbTrustCenterRequireKeyExchange;
#endif
#if (ZG_BUILD_JOINING_TYPE)
    uint8_t bdbTCLinkKeyExchangeAttemptsMax;
    bool has_bdbTCLinkKeyExchangeAttemptsMax;
    uint8_t bdbTCLinkKeyExchangeMethod;
    bool has_bdbTCLinkKeyExchangeMethod;
#endif
} zstack_bdbSetAttributesReq_t;
typedef struct _zstack_bdbgetattributesrsp_t
{
    uint32_t bdbSecondaryChannelSet;
    uint32_t bdbPrimaryChannelSet;
    uint16_t bdbCommissioningGroupID;
    uint8_t  bdbCommissioningStatus;
    uint8_t  bdbCommissioningMode;
    uint8_t  bdbNodeCommissioningCapability;
    uint8_t  bdbScanDuration;
    bool   bdbNodeIsOnANetwork;
#if (ZG_BUILD_COORDINATOR_TYPE)
    bool   bdbJoinUsesInstallCodeKey;
    uint8_t  bdbTrustCenterNodeJoinTimeout;
    bool   bdbTrustCenterRequireKeyExchange;
#endif
#if (ZG_BUILD_JOINING_TYPE)
    uint8_t  bdbNodeJoinLinkKeyType;
    uint8_t  bdbTCLinkKeyExchangeAttempts;
    uint8_t  bdbTCLinkKeyExchangeAttemptsMax;
    uint8_t  bdbTCLinkKeyExchangeMethod;
#endif
} zstack_bdbGetAttributesRsp_t;
typedef struct _zstack_bdbgetfbinitiatorstatusrsp_t
{
  uint8_t RemainingTime;
  uint8_t AttemptsLeft;
}
zstack_bdbGetFBInitiatorStatusRsp_t;
typedef struct _zstack_bdbgenerateinstallcodecrcreq_t
{
  uint8_t installCode[16];
} zstack_bdbGenerateInstallCodeCRCReq_t;
typedef struct _zstack_bdbgenerateinstallcodecrcrsp_t
{
  uint16_t CRC;
} zstack_bdbGenerateInstallCodeCRCRsp_t;
#ifdef BDB_REPORTING
typedef struct _zstack_bdbrepaddattrcfgrecorddefaulttolistreq_t
{
  uint8_t endpoint;
  uint16_t cluster;
  uint16_t attrID;
  uint16_t minReportInt;
  uint16_t maxReportInt;
  uint8_t reportableChange[8];
} zstack_bdbRepAddAttrCfgRecordDefaultToListReq_t;
typedef struct _zstack_bdbrepchangedattrvaluereq_t
{
  uint8_t endpoint;
  uint16_t cluster;
  uint16_t attrID;
} zstack_bdbRepChangedAttrValueReq_t;
typedef struct _zstack_bdbprocessinconfigreportingreq_t
{
  zclIncomingMsg_t *pZclIncommingMsg;
} zstack_bdbProcessInConfigReportReq_t;
typedef struct _zstack_bdbprocessinreadconfigreportcfgreq_t
{
  zclIncomingMsg_t *pZclIncommingMsg;
} zstack_bdbProcessInReadReportCfgReq_t;
#endif
typedef struct _zstack_bdbaddinstallcodereq_t
{
  uint8_t pInstallCode[18];
  uint8_t pExt[EXTADDR_LEN];
} zstack_bdbAddInstallCodeReq_t;
typedef struct _zstack_bdbtouchlinktargetenablecommissioningreq_t
{
  uint32_t timeoutTime;
} zstack_bdbTouchLinkTargetEnableCommissioningReq_t;
typedef struct _zstack_bdbtouchlinktargetgettimerrsp_t
{
  uint32_t Time;
} zstack_bdbTouchLinkTargetGetTimerRsp_t;
typedef struct _zstack_bdbsetactivecentralizedlinkkeyreq_t
{
  zstack_CentralizedLinkKeyModes_t zstack_CentralizedLinkKeyModes;
  uint8_t *pKey;
} zstack_bdbSetActiveCentralizedLinkKeyReq_t;
typedef struct _zstack_bdbcbketclinkkeyexchangeattemptreq_t
{
  bool didSuccess;
} zstack_bdbCBKETCLinkKeyExchangeAttemptReq_t;
typedef struct _zstack_bdbnwkdescfreereq_t
{
  networkDesc_t* nodeDescToRemove;
} zstack_bdbNwkDescFreeReq_t;
typedef struct _zstack_bdbtouchlinksetallowstealingreq_t
{
  bool allowStealing;
} zstack_bdbTouchlinkSetAllowStealingReq_t;
typedef struct _zstack_bdbtouchlinkgetallowstealingrsp_t
{
  bool allowStealing;
} zstack_bdbTouchlinkGetAllowStealingRsp_t;
typedef struct _zstack_bdbzedattemptrecovernwkrsp_t
{
  uint8_t status;
}zstack_bdbZedAttemptRecoverNwkRsp_t;
typedef struct _zstack_gpallowchangechannelreq_t
{
  uint8_t allowChangeChannel;
}zstack_gpAllowChangeChannelReq_t;
typedef struct zstackmsg_gpcommissioningmodeind_t
{
    bool isEntering;
    bool hasTime;
    uint16_t time;
}zstack_gpCommissioningModeInd_t;
#if !defined (DISABLE_GREENPOWER_BASIC_PROXY) && (ZG_BUILD_RTR_TYPE)
typedef struct _zstack_gpdataind_t
{
  gp_DataIndSecReq_t  SecReqHandling;
  uint32_t              timestamp;
  uint8_t               status;
  int8_t                Rssi;
  uint8_t               LinkQuality;
  uint8_t               SeqNumber;
  sAddr_t             srcAddr;
  uint16_t              srcPanID;
  uint8_t               appID;
  uint8_t               GPDFSecLvl;
  uint8_t               GPDFKeyType;
  bool                AutoCommissioning;
  bool                RxAfterTx;
  uint32_t              SrcId;
  uint8_t               EndPoint;
  uint32_t              GPDSecFrameCounter;
  uint8_t               GPDCmmdID;
  uint32_t              MIC;
  uint8_t               GPDasduLength;
  uint8_t               GPDasdu[1];
}zstack_gpDataInd_t;
#endif
typedef struct _zstack_gpCommissioningMode_t
{
    uint8_t isEntering;
    uint8_t hasTime;
    uint16_t time;
}zstack_gpCommissioningMode_t;
#if !defined (DISABLE_GREENPOWER_BASIC_PROXY) && (ZG_BUILD_RTR_TYPE)
typedef struct _zstack_gpSecReq_t
{
  gpdID_t      gpdID;
  uint8_t        EndPoint;
  gp_SecData_t gp_SecData;
  uint8_t        dGPStubHandle;
}zstack_gpSecReq_t;
typedef struct _zstack_gpSecRsp_t
{
  uint8_t         Status;
  uint8_t         dGPStubHandle;
  gpdID_t       gpdID;
  uint8_t         EndPoint;
  gp_SecData_t  gp_SecData;
  uint8_t         GPDKey[SEC_KEY_LEN];
}zstack_gpSecRsp_t;
#endif
typedef struct _zstack_gpcheckannounce_t
{
  uint16_t      nwkAddr;
  uint8_t       extAddr[Z_EXTADDR_LEN];
} zstack_gpCheckAnnounce_t;
typedef struct _zstack_gpaddrconflict_t
{
  uint16_t      nwkAddr;
  uint8_t       extAddr[Z_EXTADDR_LEN];
  bool        conflictResolution;
} zstack_gpAddrConflict_t;
#if !defined (DISABLE_GREENPOWER_BASIC_PROXY) && (ZG_BUILD_RTR_TYPE)
typedef struct _zstack_gpdecryptdataind_t
{
  gp_DataInd_t *pGpDataInd;
  uint8_t         key[SEC_KEY_LEN];
} zstack_gpDecryptDataInd_t;
typedef struct _zstack_gpdecryptdataindrsp_t
{
  gp_DataInd_t *pGpDataInd;
  uint8_t         status;
} zstack_gpDecryptDataIndRsp_t;
typedef struct _zstack_gpencryptdecryptcommissioningkey_t
{
  bool        encrypt;
  gpdID_t     gpdId;
  uint8_t       keyType;
  uint8_t       key[SEC_KEY_LEN];
  uint32_t      keyMic;
  uint8_t       secKey[SEC_KEY_LEN];
  uint32_t      secFrameCounter;
} zstack_gpEncryptDecryptCommissioningKey_t;
typedef struct zstack_gpcommissioningsuccess_t
{
    uint16_t       index;
    uint16_t       alias;
    gpdID_t      gpdID;
} zstack_gpCommissioningSuccess_t;
#endif
typedef struct _zstack_gpencryptdecryptcommissioningkeyrsp_t
{
  uint8_t       key[SEC_KEY_LEN];
  uint32_t      keyMic;
  uint32_t      secFrameCounter;
  uint8_t       status;
} zstack_gpEncryptDecryptCommissioningKeyRsp_t;
typedef struct _zstackmsg_gpaliasnwkaddress_t
{
    uint16_t       alias;
} zstack_gpAliasNwkAddress_t;
#if defined ( BDB_TL_INITIATOR ) || defined ( BDB_TL_TARGET )
typedef struct _zstack_tlScanReq_t
{
  afAddrType_t     addr;
  uint32_t           transID;
  uint8_t            seqNum;
}zstack_tlScanReq_t;
typedef struct _zstack_tlTargetNwkStartReq_t
{
  afAddrType_t        addr;
  bdbTLNwkStartReq_t  nwkStartReq;
  uint8_t               seqNum;
  bool                allowStealing;
}zstack_tlTargetNwkStartReq_t;
typedef struct _zstack_touchlinkNwkJoinReq_t
{
  afAddrType_t        addr;
  bdbTLNwkJoinReq_t   nwkJoinReq;
  uint8_t               seqNum;
#if defined ( BDB_TL_TARGET )
  bool                allowStealing;
#endif
}zstack_touchlinkNwkJointReq_t;
typedef struct _zstack_touchlinkNwkUpdateReq_t
{
  uint32_t        transID;
  uint8_t         extendedPANID[Z_EXTADDR_LEN];
  uint8_t         nwkUpdateId;
  uint8_t         logicalChannel;
  uint16_t        PANID;
  uint16_t        nwkAddr;
} zstack_touchlinkNwkUpdateReq_t;
typedef struct _zstack_touchlinkGetScanBaseTime_t
{
  uint16_t time;
  bool   stopTimer;
} zstack_touchlinkGetScanBaseTime_t;
typedef struct _zstack_touchlinkScanRsp_t
{
  afAddrType_t addr;
  bdbTLScanRsp_t scanRsp;
} zstack_touchlinkScanRsp_t;
typedef struct _zstack_touchlinkDevInfoRsp_t
{
  afAddrType_t addr;
  bdbTLDeviceInfoRsp_t devInfoRsp;
} zstack_touchlinkDevInfoRsp_t;
typedef struct _zstack_touchlinkNwkStartRsp_t
{
  bdbTLNwkStartRsp_t nwkStartRsp;
} zstack_touchlinkNwkStartRsp_t;
typedef struct _zstack_touchlinkNwkJoinRsp_t
{
  afAddrType_t addr;
  bdbTLNwkJoinRsp_t  nwkJoinRsp;
} zstack_touchlinkNwkJoinRsp_t;
#endif
typedef struct _zstack_secnwkkeygetrsp_t
{
    bool activeKey;
    uint8_t seqNum;
    uint8_t key[16];
} zstack_secNwkKeyGetRsp_t;
typedef struct _zstack_secapslinkkeygetrsp_t
{
    bool tcLinkKey;
    zstack_LongAddr_t ieeeAddr;
    uint8_t key[16];
    uint32_t txFrmCntr;
    uint32_t rxFrmCntr;
} zstack_secApsLinkKeyGetRsp_t;
typedef struct _zstack_defaultrsp_t
{
    zstack_ZStatusValues status;
} zstack_DefaultRsp_t;
typedef struct _zstack_pauseResumeDeviceReq_t
{
    bool pause;
} zstack_pauseResumeDeviceReq_t;
#ifdef __cplusplus
}
#endif
