blkburn/cc2652_zigbee_zed/zed_sensor_cc2652/Stack/sys/zglobals.h

#define ZGLOBALS_H
#ifdef __cplusplus
extern "C" {
#endif
#include "zcomdef.h"
#if defined( BUILD_ALL_DEVICES ) && !defined( ZSTACK_DEVICE_BUILD )
  #define ZSTACK_DEVICE_BUILD  (DEVICE_BUILD_COORDINATOR | DEVICE_BUILD_ROUTER | DEVICE_BUILD_ENDDEVICE)
#endif
#if !defined ( ZSTACK_DEVICE_BUILD )
  #if defined ( ZDO_COORDINATOR )
    #define ZSTACK_DEVICE_BUILD  (DEVICE_BUILD_COORDINATOR)
  #elif defined ( RTR_NWK )
    #define ZSTACK_DEVICE_BUILD  (DEVICE_BUILD_ROUTER)
  #else
    #define ZSTACK_DEVICE_BUILD  (DEVICE_BUILD_ENDDEVICE)
  #endif
#endif
#define ZG_BUILD_COORDINATOR_TYPE  (ZSTACK_DEVICE_BUILD & DEVICE_BUILD_COORDINATOR)
#define ZG_BUILD_RTR_TYPE          (ZSTACK_DEVICE_BUILD & (DEVICE_BUILD_COORDINATOR | DEVICE_BUILD_ROUTER))
#define ZG_BUILD_ENDDEVICE_TYPE    (ZSTACK_DEVICE_BUILD & DEVICE_BUILD_ENDDEVICE)
#define ZG_BUILD_RTRONLY_TYPE      (ZSTACK_DEVICE_BUILD == DEVICE_BUILD_ROUTER)
#define ZG_BUILD_JOINING_TYPE      (ZSTACK_DEVICE_BUILD & (DEVICE_BUILD_ROUTER | DEVICE_BUILD_ENDDEVICE))
#define ZG_BUILD_ALL_DEVICES_TYPE  (ZSTACK_DEVICE_BUILD & (DEVICE_BUILD_COORDINATOR | DEVICE_BUILD_ROUTER | DEVICE_BUILD_ENDDEVICE))
#if ( ZSTACK_DEVICE_BUILD == DEVICE_BUILD_COORDINATOR )
  #define ZG_DEVICE_COORDINATOR_TYPE 1
#else
  #define ZG_DEVICE_COORDINATOR_TYPE (zgDeviceLogicalType == ZG_DEVICETYPE_COORDINATOR)
#endif
#if ( ZSTACK_DEVICE_BUILD == (DEVICE_BUILD_ROUTER | DEVICE_BUILD_COORDINATOR) )
  #define ZG_DEVICE_RTR_TYPE 1
#else
  #define ZG_DEVICE_RTR_TYPE ((zgDeviceLogicalType == ZG_DEVICETYPE_COORDINATOR) || (zgDeviceLogicalType == ZG_DEVICETYPE_ROUTER))
#endif
#if ( ZSTACK_DEVICE_BUILD == DEVICE_BUILD_ROUTER )
  #define ZG_DEVICE_RTRONLY_TYPE  1
#else
  #define ZG_DEVICE_RTRONLY_TYPE (zgDeviceLogicalType == ZG_DEVICETYPE_ROUTER)
#endif
#if ( ZSTACK_DEVICE_BUILD == DEVICE_BUILD_ENDDEVICE )
  #define ZG_DEVICE_ENDDEVICE_TYPE 1
#else
  #define ZG_DEVICE_ENDDEVICE_TYPE (zgDeviceLogicalType == ZG_DEVICETYPE_ENDDEVICE)
#endif
#define ZG_DEVICE_JOINING_TYPE     ((zgDeviceLogicalType == ZG_DEVICETYPE_ROUTER) || (zgDeviceLogicalType == ZG_DEVICETYPE_ENDDEVICE))
#if ( ZG_BUILD_RTR_TYPE )
  #if ( ZG_BUILD_ENDDEVICE_TYPE )
    #define ZSTACK_ROUTER_BUILD         (ZG_BUILD_RTR_TYPE && ZG_DEVICE_RTR_TYPE)
  #else
    #define ZSTACK_ROUTER_BUILD         1
  #endif
#else
  #define ZSTACK_ROUTER_BUILD           0
#endif
#if ( ZG_BUILD_ENDDEVICE_TYPE )
  #if ( ZG_BUILD_RTR_TYPE )
    #define ZSTACK_END_DEVICE_BUILD     (ZG_BUILD_ENDDEVICE_TYPE && ZG_DEVICE_ENDDEVICE_TYPE)
  #else
    #define ZSTACK_END_DEVICE_BUILD     1
  #endif
#else
  #define ZSTACK_END_DEVICE_BUILD       0
#endif
  #define BUILD_FLEXABLE 0
#define BEACON_MESH 0
#define ZG_DEVICETYPE_COORDINATOR      0x00
#define ZG_DEVICETYPE_ROUTER           0x01
#define ZG_DEVICETYPE_ENDDEVICE        0x02
  #if ( ZG_BUILD_COORDINATOR_TYPE )
    #define DEVICE_LOGICAL_TYPE ZG_DEVICETYPE_COORDINATOR
  #elif ( ZG_BUILD_RTR_TYPE )
    #define DEVICE_LOGICAL_TYPE ZG_DEVICETYPE_ROUTER
  #elif ( ZG_BUILD_ENDDEVICE_TYPE )
    #define DEVICE_LOGICAL_TYPE ZG_DEVICETYPE_ENDDEVICE
  #else
    #error ZSTACK_DEVICE_BUILD must be defined as something!
  #endif
  #define MAX_MISSING_MAC_ACK_LINK_FAILURE 3
  #define MAX_DATA_RETRIES         2
  #define MAX_BCAST_RETRIES        2
  #define PASSIVE_ACK_TIMEOUT      5
  #define BCAST_DELIVERY_TIME      30
  #define ROUTE_DISCOVERY_TIME     5
  #define APS_DEFAULT_MAXBINDING_TIME 16000
  #define APS_DEFAULT_NONMEMBER_RADIUS   2
  #define APSF_DEFAULT_WINDOW_SIZE       1
  #define APSF_DEFAULT_INTERFRAME_DELAY  50
  #define CONCENTRATOR_ENABLE          false // true if concentrator is enabled
  #define CONCENTRATOR_DISCOVERY_TIME  0
  #define CONCENTRATOR_RADIUS          0x0a
  #define CONCENTRATOR_ROUTE_CACHE     false // true if concentrator has route cache
  #define START_DELAY                  0x0a
  #define SAPI_ENDPOINT                0xe0
#define ZG_STARTUP_CLEAR               0x00
#define ZG_STARTUP_SET                 0xFF
#if defined ( AMI_PROFILE ) || defined ( SE_PROFILE )
#define TC_LINKKEY_JOIN
#endif
  #define APS_DUP_REJ_ENTRIES                     5
  #define DEFAULT_APS_DUP_REJ_TIMEOUT_INCREMENT   1000
  #define DEFAULT_APS_DUP_REJ_TIMEOUT             10
  #define NWK_END_DEVICE_LEAVE_TIMEOUT 9
  #define END_DEV_CONFIGURATION   0     // Per ZigBee Core spec R21, 0 is the only valid value
  #define END_DEVICE_KEEP_ALIVE_MESSAGES_PER_TIMEOUT    3
#if (END_DEVICE_KEEP_ALIVE_MESSAGES_PER_TIMEOUT==0)
  #error "Invalid valid value for END_DEVICE_KEEP_ALIVE_MESSAGES_PER_TIMEOUT"
#endif
#define MAX_SUPPORTED_ENDPOINTS 5
#define BDB_MAX_SECURE_REJOIN_ATTEMPTS 3
#define BDB_ATTEMPT_UNSECURE_REJOIN TRUE
#define ZG_UNIQUE_LINK_KEY        0x00
#define ZG_GLOBAL_LINK_KEY        0x01
#define ZG_PROVISIONAL_KEY          0x00  //Used for IC derived keys
#define ZG_UNVERIFIED_KEY           0x01  //Unique key that is not verified
#define ZG_VERIFIED_KEY             0x02  //Unique key that got verified by ZC
#define ZG_DISTRIBUTED_DEFAULT_KEY  0xFC  //Use default key to join
#define ZG_NON_R21_NWK_JOINED       0xFD  //Joined a network which is not R21 nwk, so TCLK process finished.
#define ZG_VERIFIED_KEY_JOINING_DEV 0xFE  //Unique key that got verified by Joining device. This means that key is stored as plain text (not seed hashed)
#define ZG_DEFAULT_KEY              0xFF  //Entry using default key
#define ZG_IC_NOT_SUPPORTED           0x00
#define ZG_IC_SUPPORTED_NOT_REQUIRED  0x01
#define ZG_IC_MUST_USED               0x02
extern uint8_t zgMaxDataRetries;
extern uint8_t zgMaxMissingMacAckLinkFailure;
extern uint32_t zgDefaultChannelList;
#define zgDefaultStartingScanDuration  bdbAttributes.bdbScanDuration
extern uint8_t zgStackProfile;
extern uint8_t zgIndirectMsgTimeout;
extern uint8_t zgSecurePermitJoin;
extern uint8_t zgAllowRejoinsWithWellKnownKey;
extern uint8_t zgAllowInstallCodes;
extern uint8_t zgAllowRemoteTCPolicyChange;
extern uint8_t zgApsTrustCenterAddr[];
extern uint8_t zgRouteDiscoveryTime;
extern uint8_t zgRouteExpiryTime;
extern uint8_t zgExtendedPANID[];
extern uint8_t zgMaxBcastRetires;
extern uint8_t zgPassiveAckTimeout;
extern uint8_t zgBcastDeliveryTime;
extern uint8_t zgConcentratorEnable;
extern uint8_t zgConcentratorDiscoveryTime;
extern uint8_t zgConcentratorRadius;
extern uint8_t zgConcentratorRC;
extern uint8_t zgNwkSrcRtgExpiryTime;
extern uint8_t zgRouterOffAssocCleanup;
extern uint8_t zgNwkLeaveRequestAllowed;
extern uint8_t zgNwkProcessLocalLeaveCnf;
extern uint8_t zgNwkParentInformation;
extern uint8_t zgNwkEndDeviceTimeoutDefault;
extern uint8_t zgNwkEndDeviceLeaveTimeoutDefault;
extern uint8_t zgEndDeviceKeepAliveMessagesPerTimeout;
extern uint8_t zgEndDeviceTimeoutValue;
extern uint8_t zgEndDeviceConfiguration;
extern uint8_t zgChildAgingEnable;
extern uint8_t zTouchLinkNwkStartRtr;
extern uint8_t zgAllowRadioRxOff;
extern uint8_t  zgApscMaxFrameRetries;
extern uint16_t zgApscAckWaitDurationPolled;
extern uint8_t  zgApsAckWaitMultiplier;
extern uint16_t zgApsDefaultMaxBindingTime;
extern uint8_t  zgApsUseExtendedPANID[Z_EXTADDR_LEN];
extern uint8_t  zgApsUseInsecureJoin;
extern uint8_t  zgApsNonMemberRadius;
extern uint16_t zgApscDupRejTimeoutInc;
extern uint8_t  zgApscDupRejTimeoutCount;
extern uint16_t zgApsMinDupRejTableSize;
extern uint8_t zgPreConfigKeys;
extern uint8_t zgApsLinkKeyType;
extern uint8_t zgUseDefaultTCLK;
#if defined ( APP_TP2_TEST_MODE )
#define TP_GU_ALL            0
#define TP_GU_SEC_ONLY       1
#define TP_GU_NONSEC_ONLY    2
#define TP_GU_BOTH           2   // use both NoAPS and APS security
extern uint8_t guTxApsSecON;
extern uint8_t guEnforceRxApsSec;
#endif
extern uint8_t zgApsAllowR19Sec;
extern uint8_t zgSwitchCoordKey;
extern uint8_t zgSwitchCoordKeyIndex;
extern uint16_t zgConfigPANID;
extern uint8_t  zgDeviceLogicalType;
extern uint8_t  zgNwkMgrMinTransmissions;
#if !defined MT_TASK
extern uint8_t zgZdoDirectCB;
#endif
extern uint8_t zgBdbAttemptUnsecureRejoin;
extern uint8_t zgBdbMaxSecureRejoinAttempts;
extern uint8_t zgNwkMgrMode;
extern uint8_t zgInit( void );
extern void zgInitItems( uint8_t setDefault );
extern uint8_t zgReadStartupOptions( void );
extern uint8_t zgWriteStartupOptions( uint8_t action, uint8_t bitOptions );
extern void zgSetItem( uint16_t id, uint16_t len, void *buf );
#ifdef __cplusplus
}
#endif
