blkburn/cc2652_zigbee_zed/zed_sensor_cc2652/Common/zcl/zcl.h

/**************************************************************************************************
  Filename:       zcl.h
  Revised:        $Date: 2014-11-25 09:19:55 -0800 (Tue, 25 Nov 2014) $
  Revision:       $Revision: 41240 $

  Description:    This file contains the Zigbee Cluster Library Foundation definitions.


  Copyright (c) 2019, Texas Instruments Incorporated
  All rights reserved.

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
  *  Neither the name of Texas Instruments Incorporated nor the names of
      its contributors may be used to endorse or promote products derived
      from this software without specific prior written permission.

  THIS SOFTWARE IS PROVIDED BY THE COPYRIGHT HOLDERS AND CONTRIBUTORS "AS IS"
  AND ANY EXPRESS OR IMPLIED WARRANTIES, INCLUDING, BUT NOT LIMITED TO,
  THE IMPLIED WARRANTIES OF MERCHANTABILITY AND FITNESS FOR A PARTICULAR
  PURPOSE ARE DISCLAIMED. IN NO EVENT SHALL THE COPYRIGHT OWNER OR
  CONTRIBUTORS BE LIABLE FOR ANY DIRECT, INDIRECT, INCIDENTAL, SPECIAL,
  EXEMPLARY, OR CONSEQUENTIAL DAMAGES (INCLUDING, BUT NOT LIMITED TO,
  PROCUREMENT OF SUBSTITUTE GOODS OR SERVICES; LOSS OF USE, DATA, OR PROFITS;
  OR BUSINESS INTERRUPTION) HOWEVER CAUSED AND ON ANY THEORY OF LIABILITY,
  WHETHER IN CONTRACT, STRICT LIABILITY, OR TORT (INCLUDING NEGLIGENCE OR
  OTHERWISE) ARISING IN ANY WAY OUT OF THE USE OF THIS SOFTWARE,
  EVEN IF ADVISED OF THE POSSIBILITY OF SUCH DAMAGE.
**************************************************************************************************/

/**
 *  @defgroup ZCL ZCL
 *  @brief This module implements the Zigbee Cluster Library
 *  @{
 *
 *  @file  zcl.h
 *  @brief      Top level ZCL header
 */


#ifndef ZCL_H
#define ZCL_H

#if defined ( BDB_REPORTING )
#ifndef ZCL_REPORTING_DEVICE
  #define ZCL_REPORTING_DEVICE
#endif
#endif

#ifdef __cplusplus
extern "C"
{
#endif

/*********************************************************************
 * INCLUDES
 */
#if !defined ( ZCL_STANDALONE ) || defined ( ZCL_STANDALONE_OSAL )
  #include "osal.h"
  #include "osal_nv.h"
  #include "osal_tasks.h"
#endif

#include "af.h"
#include "aps_groups.h"
#include "ti_zstack_config.h"

/*********************************************************************
 * CONSTANTS
 */

/**
 * @defgroup ZCL_CLUSTER_IDS ZCL Cluster IDs
 * @{
 */

/**
 * @defgroup ZCL_GENERAL_CLUSTER_IDS ZCL General Clusters
 * @{
 * @brief This group defines the IDs for the General Clusters
 * defined in the ZCL v7 specification
 */
/// Basic Cluster. Attributes for determining basic information about a device,
/// setting user device information such as description of location, and
/// enabling a device.
#define ZCL_CLUSTER_ID_GENERAL_BASIC                             0x0000
/// Power Configuration Cluster. Attributes for determining more detailed
/// information about a device's power source(s), and for configuring
/// under/over voltage alarms.
#define ZCL_CLUSTER_ID_GENERAL_POWER_CFG                         0x0001
/// Device Temperature Configuration Cluster. Attributes for determining
/// information about a device's internal temperature, and for configuring
/// under/over temperature alarms.
#define ZCL_CLUSTER_ID_GENERAL_DEVICE_TEMP_CONFIG                0x0002
/// Identify Cluster. Attributes and commands for putting a device into
/// Identification mode (e.g., flashing a light).
#define ZCL_CLUSTER_ID_GENERAL_IDENTIFY                          0x0003
/// Groups Cluster. Attributes and commands for allocating a device to one or
/// more of a number of groups of devices, where each group is addressable by a group address
#define ZCL_CLUSTER_ID_GENERAL_GROUPS                            0x0004
/// Scenes Cluster. Attributes and commands for setting up and recalling a number
/// of scenes for a device. Each scene corresponds to a set of stored values of
/// specified device attributes.
#define ZCL_CLUSTER_ID_GENERAL_SCENES                            0x0005
/// On/Off Cluster. Attributes and commands for switching devices between 'On'
/// and 'Off' states.
#define ZCL_CLUSTER_ID_GENERAL_ON_OFF                            0x0006
/// On/Off Switch Configuration Cluster. Attributes and commands for configuring
/// on/off switching devices.
#define ZCL_CLUSTER_ID_GENERAL_ON_OFF_SWITCH_CONFIGURATION       0x0007
/// Level Control Cluster. Attributes and commands for controlling a characteristic
/// of devices that can be set to a level between fully 'On' and fully 'Off'.
#define ZCL_CLUSTER_ID_GENERAL_LEVEL_CONTROL                     0x0008
/// Alarms Cluster. Attributes and commands for sending alarm notifications and
/// configuring alarm functionality.
#define ZCL_CLUSTER_ID_GENERAL_ALARMS                            0x0009
/// Time Cluster. Attributes and commands that provide an interface to a
/// real-time clock.
#define ZCL_CLUSTER_ID_GENERAL_TIME                              0x000A
/// RSSI Location Cluster. Attributes and commands for exchanging location information
/// and channel parameters among devices, and (optionally) reporting data to a
/// centralized device that collects data from devices in the network and calculates
/// their positions from the set of collected data.
#define ZCL_CLUSTER_ID_GENERAL_LOCATION                          0x000B
/// Diagnostics Cluster. Attributes and commands that provide an interface to
/// diagnostics of the stack.
#define ZCL_CLUSTER_ID_HA_DIAGNOSTIC                             0x0B05
/// Poll Control Cluster. Attributes and commands that provide an interface to
/// control the polling of sleeping end device.
#define ZCL_CLUSTER_ID_GENERAL_POLL_CONTROL                      0x0020
/// Power Profile Cluster. Attributes and commands that provide an interface to
/// the power profile of a device.
#define ZCL_CLUSTER_ID_GENERAL_POWER_PROFILE                     0x001A
/// Meter Identification Cluster. Attributes and commands that provide an interface
/// to meter identification.
#define ZCL_CLUSTER_ID_HA_METER_IDENTIFICATION                   0x0B01
/// Analog Input (basic) Cluster. An interface for reading the value of an analog
/// measurement and accessing various characteristics of that measurement.
#define ZCL_CLUSTER_ID_GENERAL_ANALOG_INPUT_BASIC                0x000C
/// Analog Output (basic) Cluster. An interface for setting the value of an analog
/// output (typically to the environment) and accessing various characteristics
/// of that value.
#define ZCL_CLUSTER_ID_GENERAL_ANALOG_OUTPUT_BASIC               0x000D
/// Analog Value (basic) Cluster. An interface for setting an analog value,
/// typically used as a control system parameter, and accessing various
/// characteristics of that value.
#define ZCL_CLUSTER_ID_GENERAL_ANALOG_VALUE_BASIC                0x000E
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
